studiohsoftware/6WLS/2WLS-30W-bottom.png

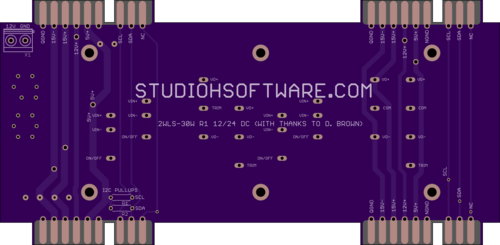
2WLS-30W-bottom.png
