studiohsoftware/6WLS/2WLS-PASSIVE-bottom.png

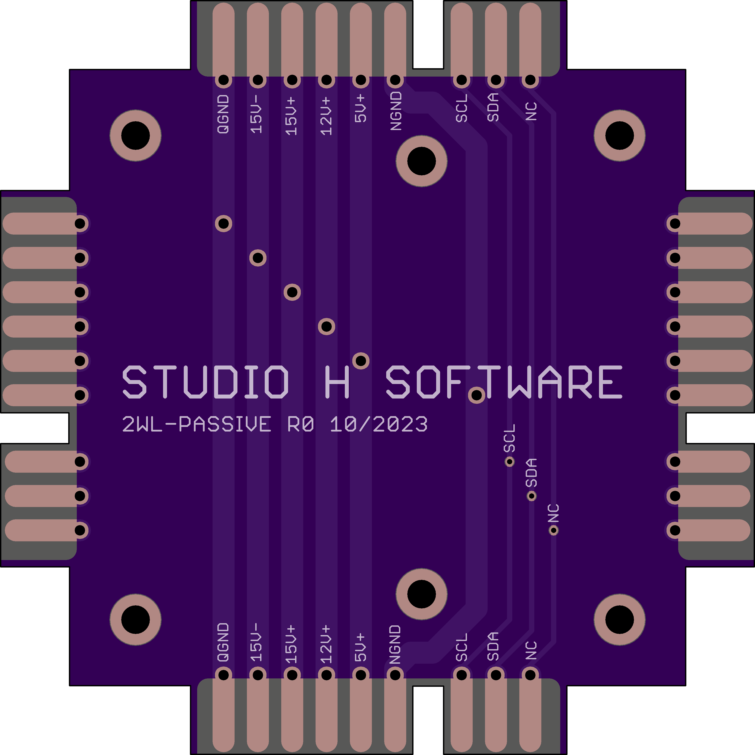
2WLS-PASSIVE-bottom.png
