studiohsoftware/6WLS/6WLS-30W-bottom.png

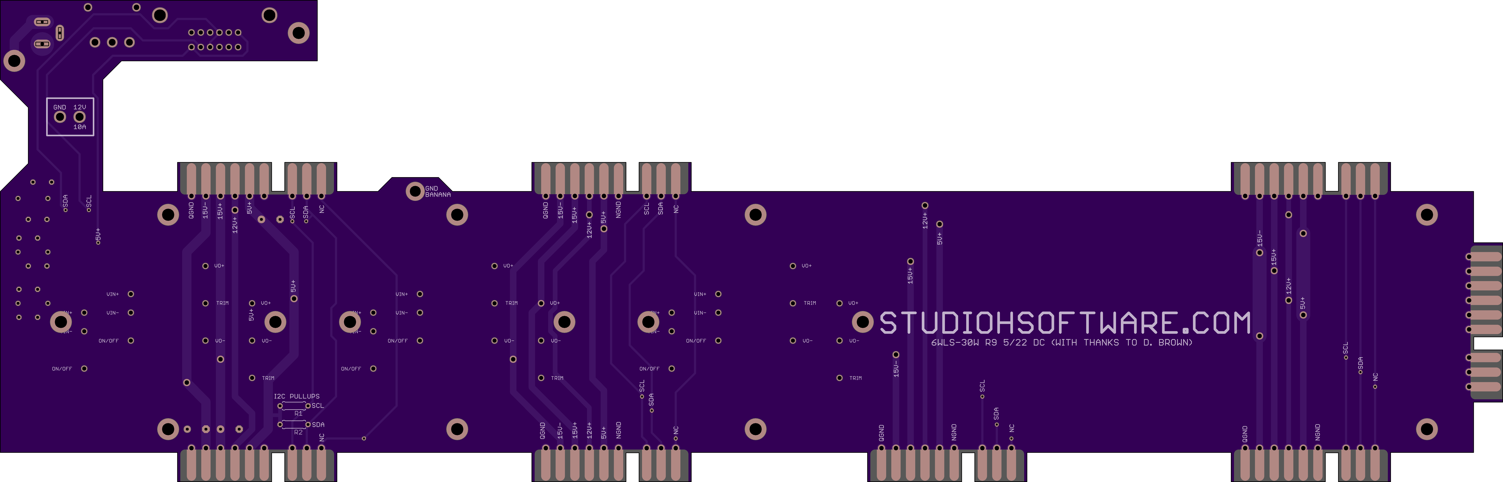
6WLS-30W-bottom.png
