studiohsoftware/6WLS/6WLS-30W-top.png

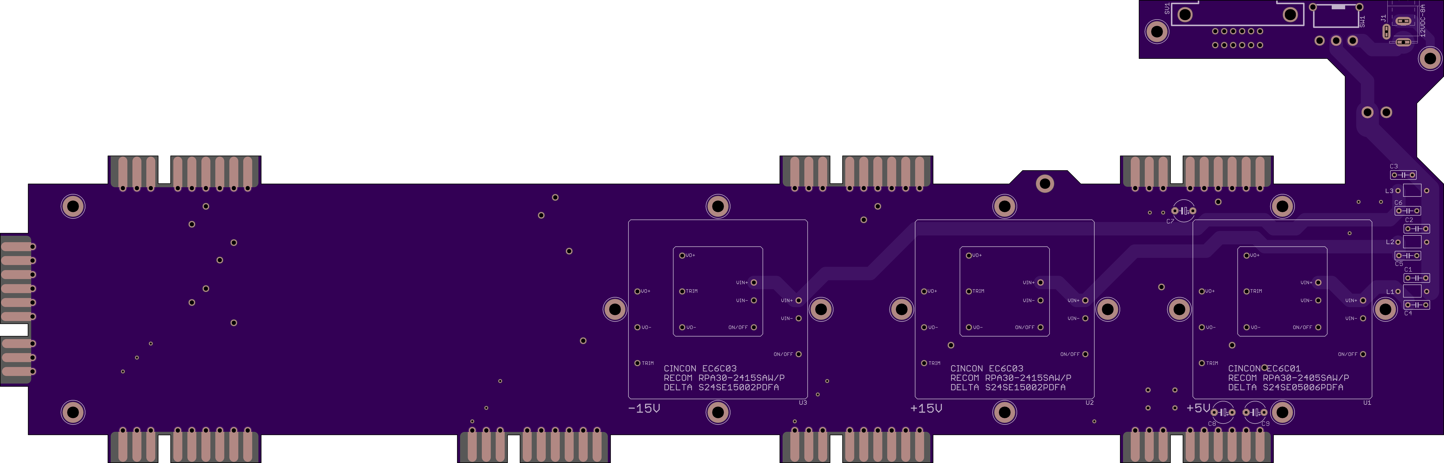
6WLS-30W-top.png
