studiohsoftware/6WLS/6WLS-40W-top.png

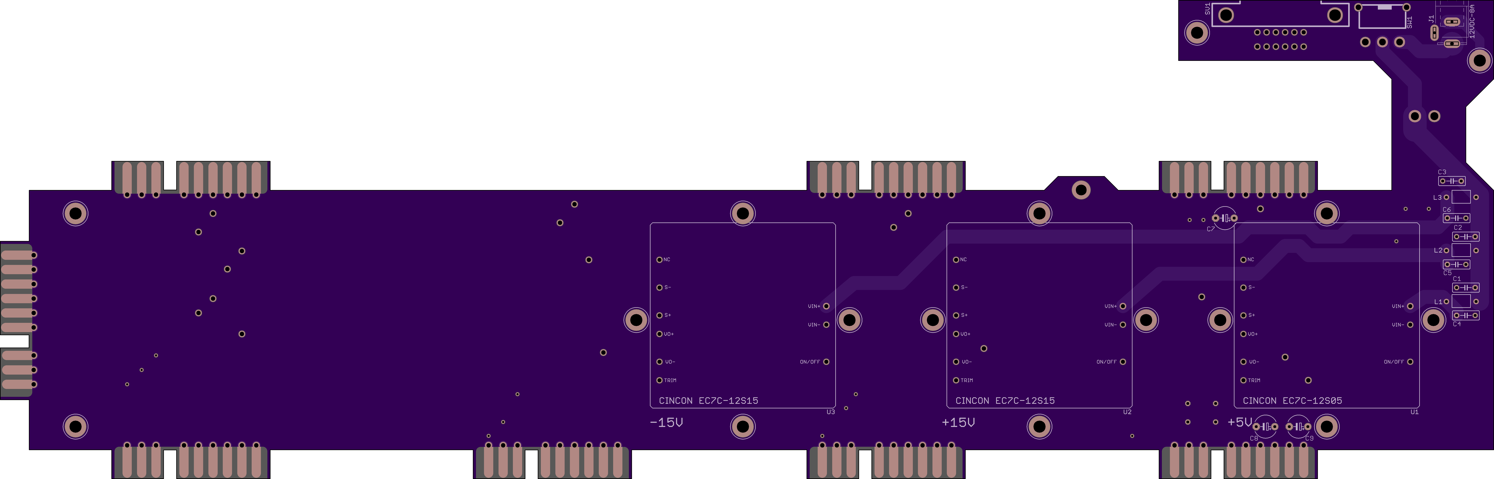
6WLS-40W-top.png
