studiohsoftware/6WLS/6WLS-PASSIVE-bottom.png

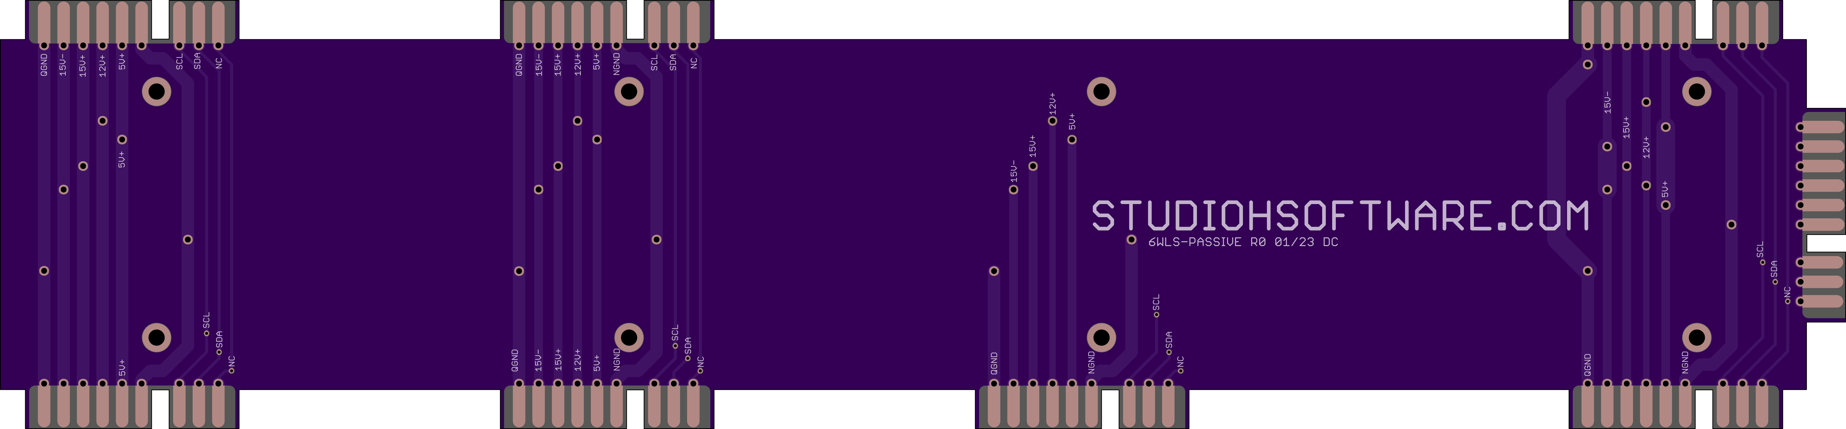
6WLS-PASSIVE-bottom.png
